Grupo-Monitor-Bodega/monitor_warehouse_master/resources/img/PCBSoldadura.png

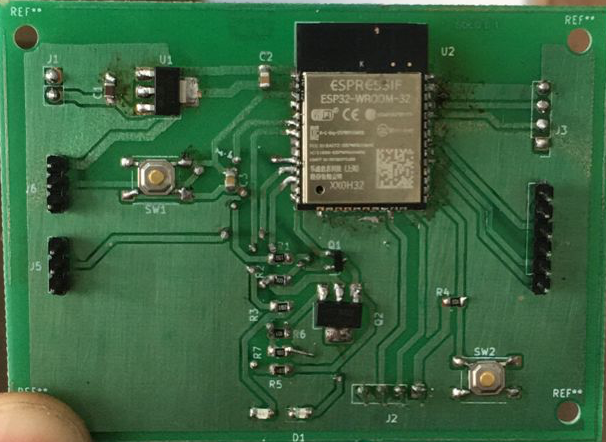
resources/img/PCBSoldadura.png
