Grupo-Monitor-Bodega/monitor_warehouse_master/resources/img/schema_embebed_project.png

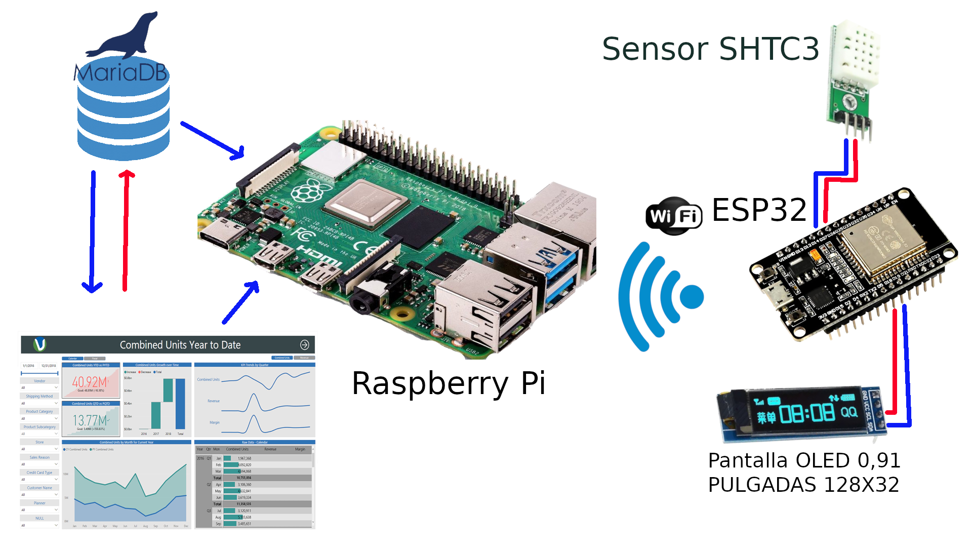
resources/img/schema_embebed_project.png
