Grupo-Monitor-Bodega/monitor_warehouse_master/resources/img/3DPCB01.png

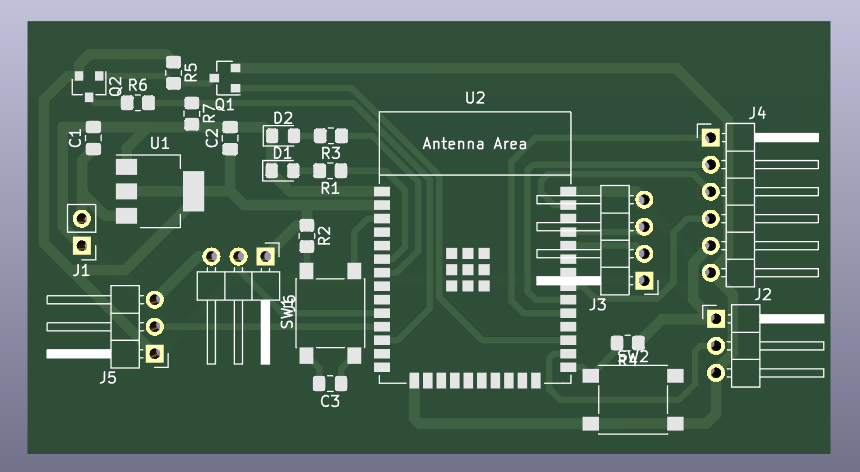
resources/img/3DPCB01.png
