Grupo-Monitor-Bodega/monitor_warehouse_master/resources/img/ConexionLeds-Batería.png

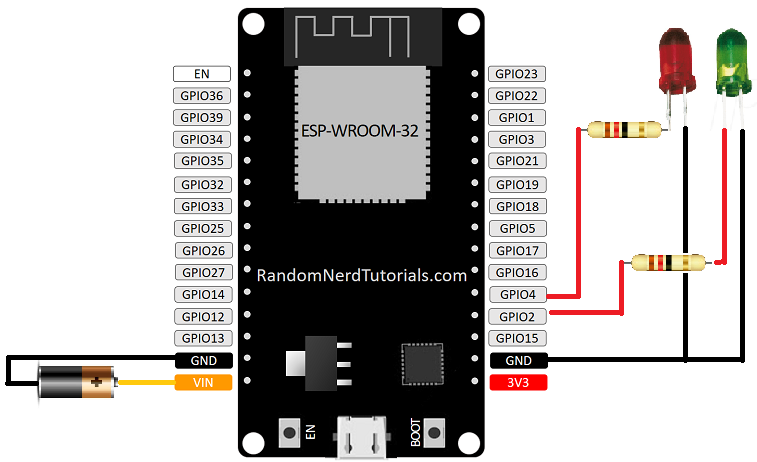
resources/img/ConexionLeds-Batería.png
