Grupo-Monitor-Bodega/monitor_warehouse_master/resources/img/ConexionSD.png

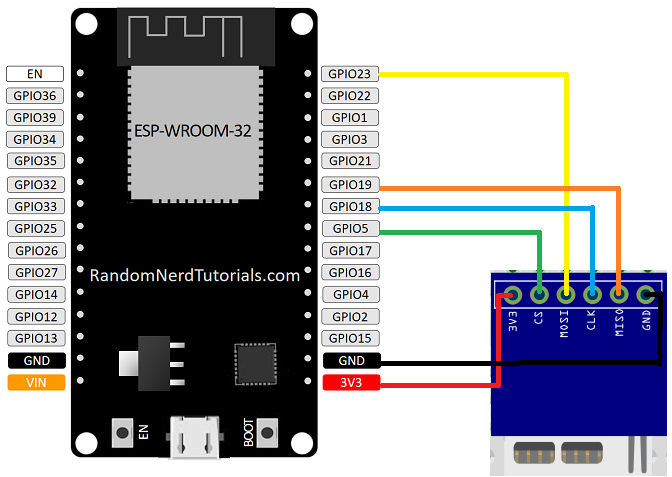
resources/img/ConexionSD.png
