Grupo-Monitor-Bodega/monitor_warehouse_master/resources/img/ConexionSensor.png

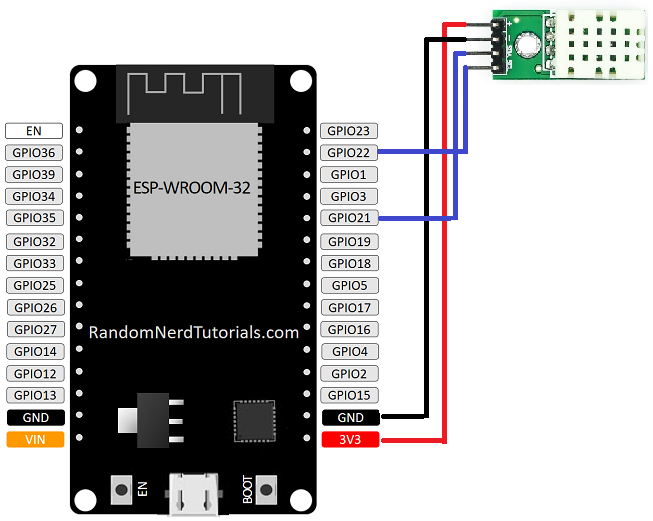
resources/img/ConexionSensor.png
