Grupo-Monitor-Bodega/monitor_warehouse_master/resources/img/Diag_bloques.png

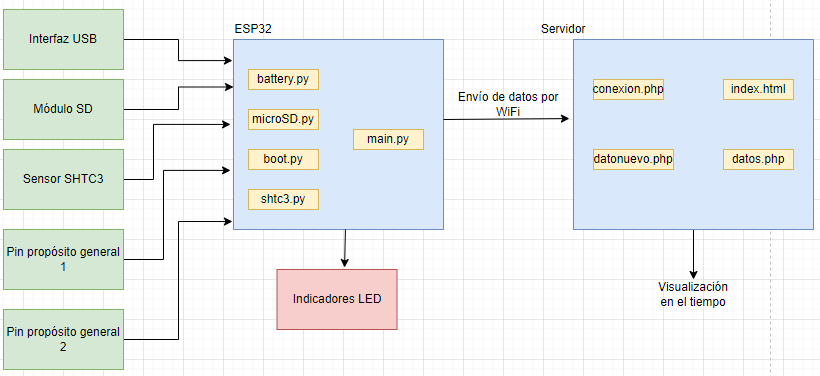
resources/img/Diag_bloques.png
