Grupo-Monitor-Bodega/monitor_warehouse_master/resources/img/esptool.png

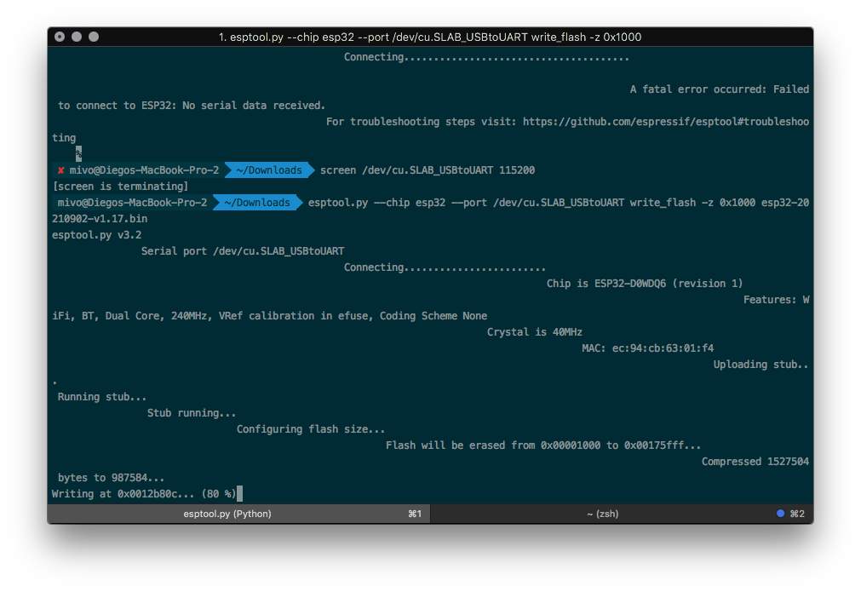
resources/img/esptool.png
