Grupo-Monitor-Bodega/monitor_warehouse_master/resources/img/FinalSchematic2.png

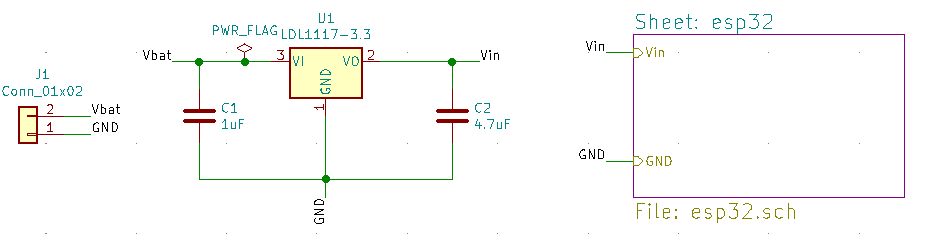
resources/img/FinalSchematic2.png
