Grupo-Monitor-Bodega/monitor_warehouse_master/resources/img/monitor_diagram.drawio.png

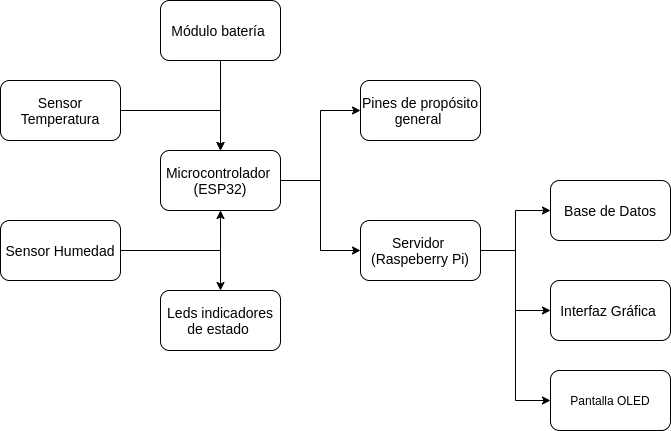
resources/img/monitor_diagram.drawio.png
