Grupo-Monitor-Bodega/monitor_warehouse_master/resources/img/pcb1.png

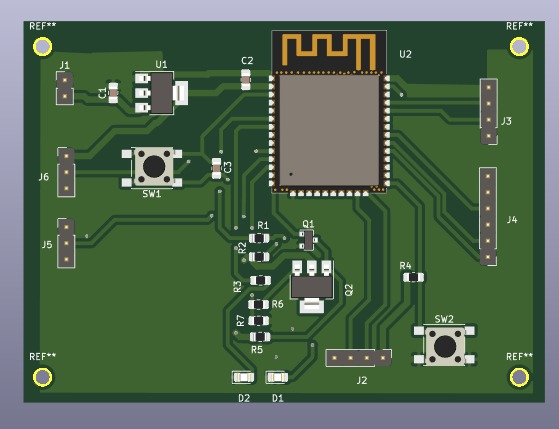
resources/img/pcb1.png
