Grupo-Monitor-Bodega/monitor_warehouse_master/resources/img/PCB01.png

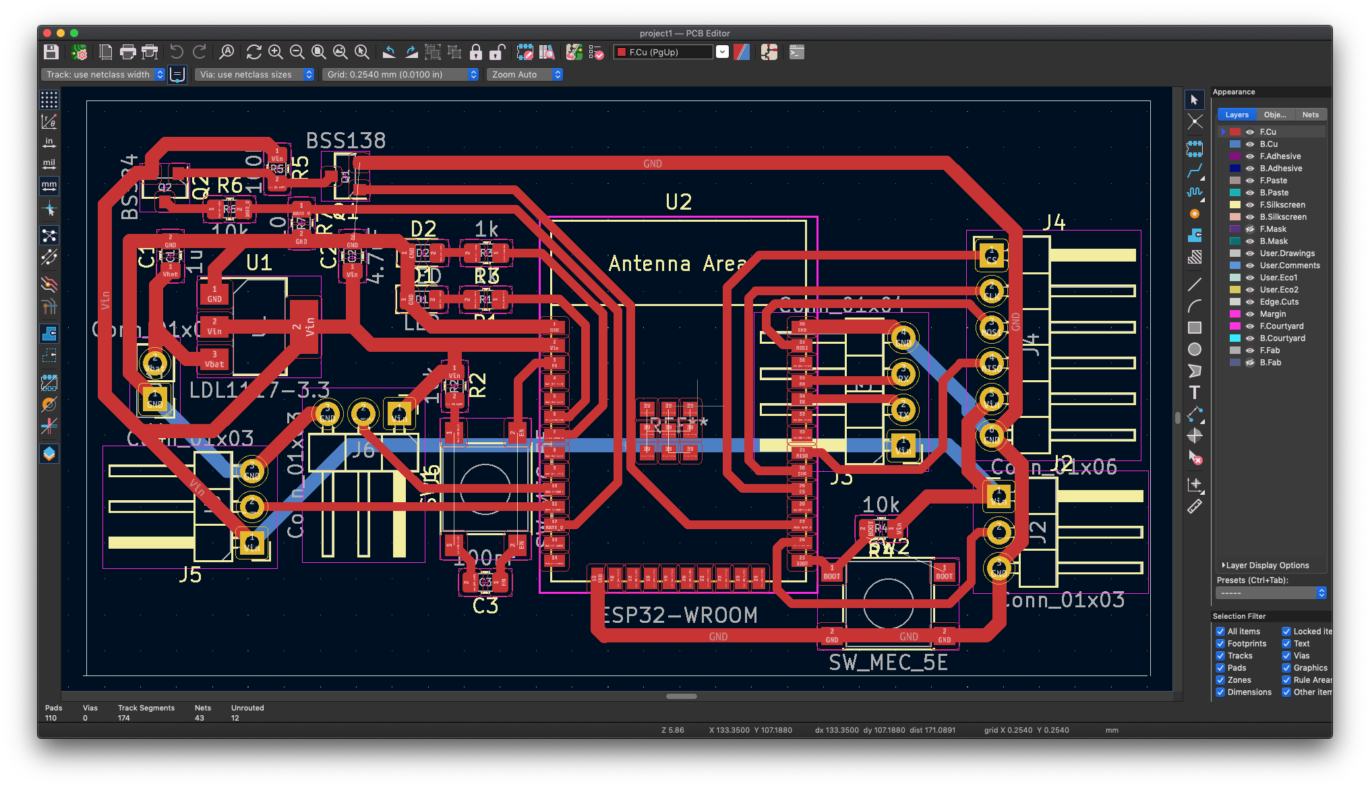
resources/img/PCB01.png
