Grupo-Monitor-Bodega/monitor_warehouse_master/resources/img/pcb2.png

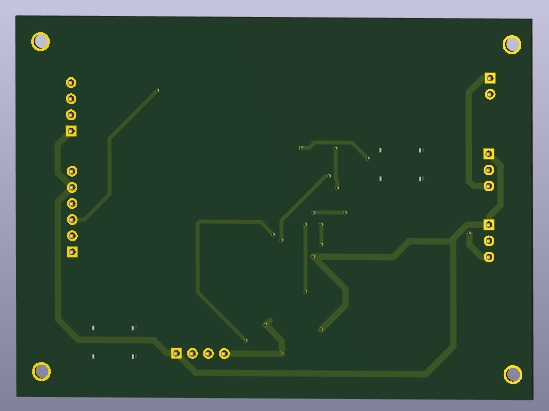
resources/img/pcb2.png
