Grupo-Monitor-Bodega/monitor_warehouse_master/resources/img/pcb3.png

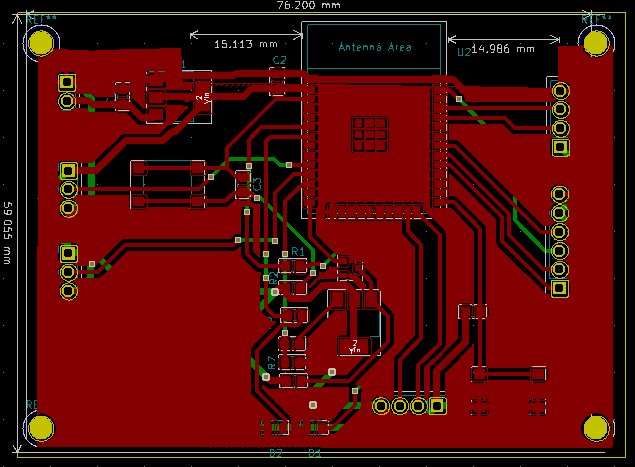
resources/img/pcb3.png
