Grupo-Monitor-Bodega/monitor_warehouse_master/resources/img/pcb4.png

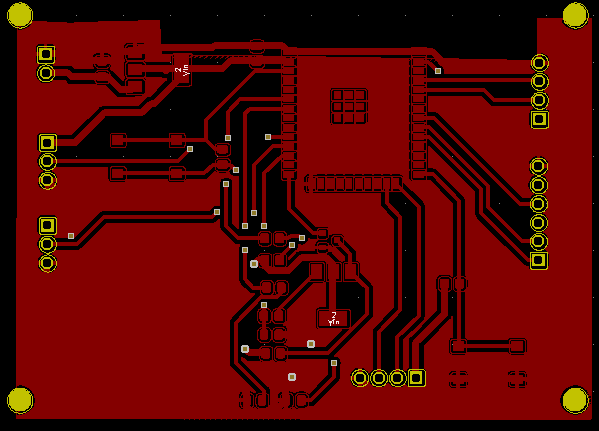
resources/img/pcb4.png
