Grupo-Monitor-Bodega/monitor_warehouse_master/resources/img/pcb5.png

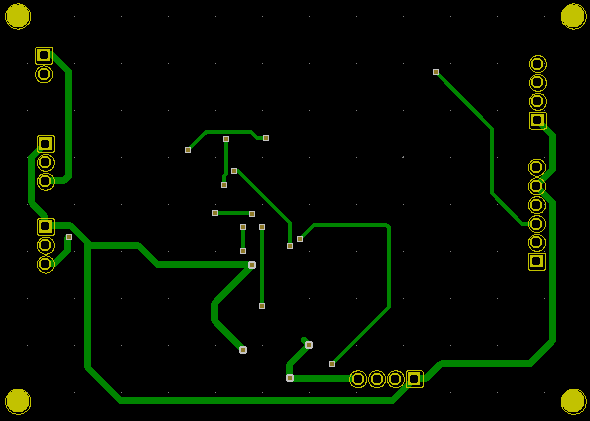
resources/img/pcb5.png
