Grupo-Monitor-Bodega/monitor_warehouse_master/resources/img/pcb6.png

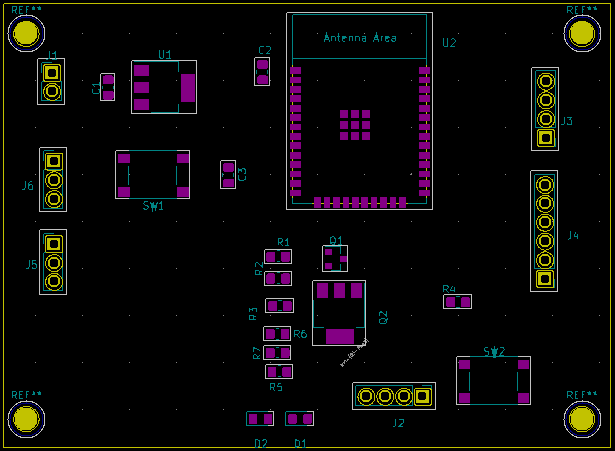
resources/img/pcb6.png
