Grupo-Monitor-Bodega/monitor_warehouse_master/resources/img/pcb7.png

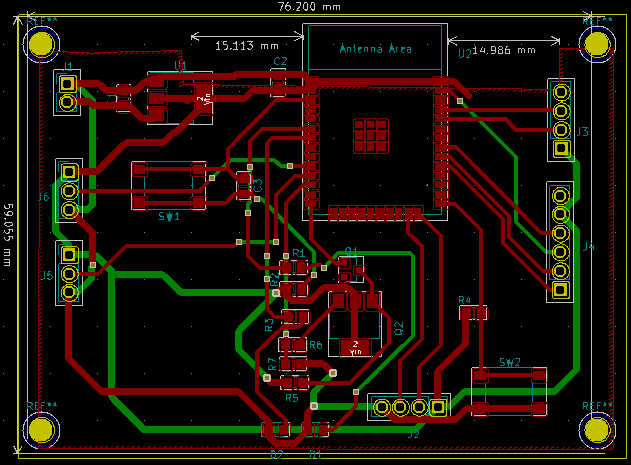
resources/img/pcb7.png
