Grupo-Monitor-Bodega/monitor_warehouse_master/resources/img/pcb8.png

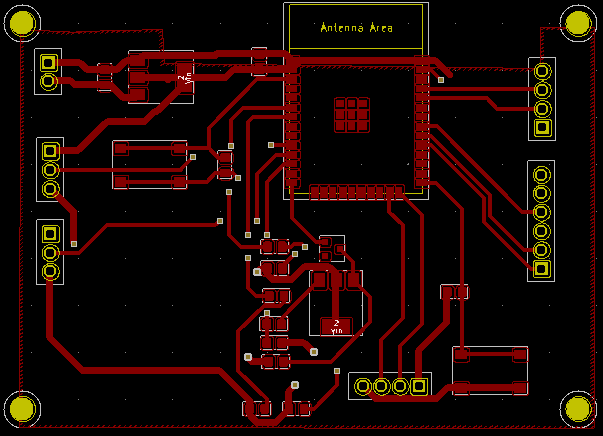
resources/img/pcb8.png
