Grupo-Monitor-Bodega/monitor_warehouse_master/resources/img/PCBdone1.jpeg

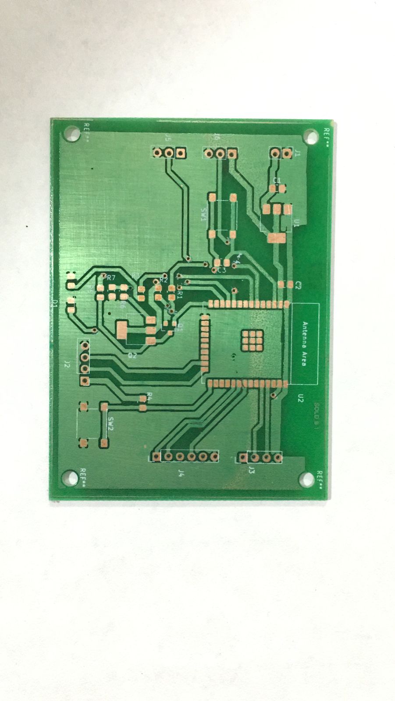
resources/img/PCBdone1.jpeg
