Grupo-Monitor-Bodega/monitor_warehouse_master/resources/img/PCBdone2.jpeg

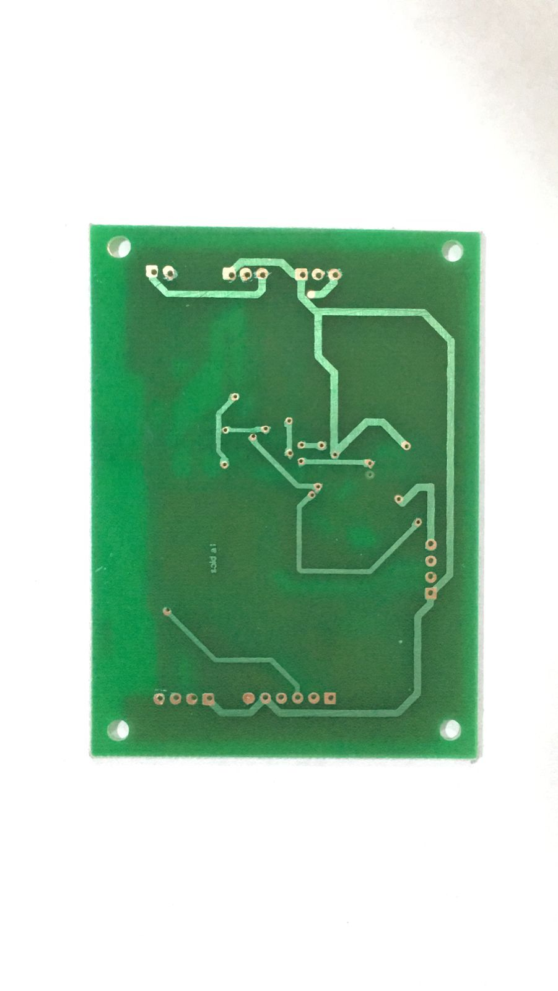
resources/img/PCBdone2.jpeg
