Grupo-Monitor-Bodega/monitor_warehouse_master/resources/img/Schematic4.png

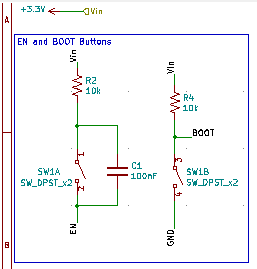
resources/img/Schematic4.png
