Grupo-Monitor-Bodega/monitor_warehouse_master/resources/img/Schematic5.png

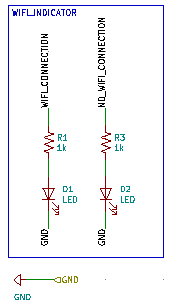
resources/img/Schematic5.png
