Grupo-Monitor-Bodega/monitor_warehouse_master/resources/img/Schematic8.png

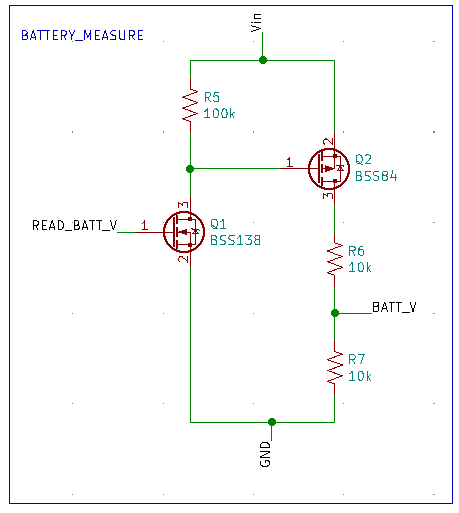
resources/img/Schematic8.png
