Grupo-Monitor-Bodega/monitor_warehouse_master/resources/img/screen.png

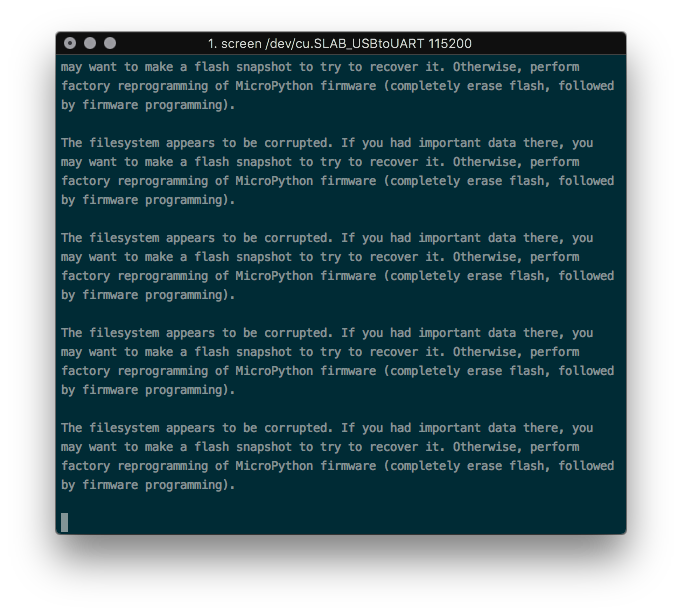
resources/img/screen.png
