Grupo-Monitor-Bodega/monitor_warehouse_master/resources/img/Servidor.png

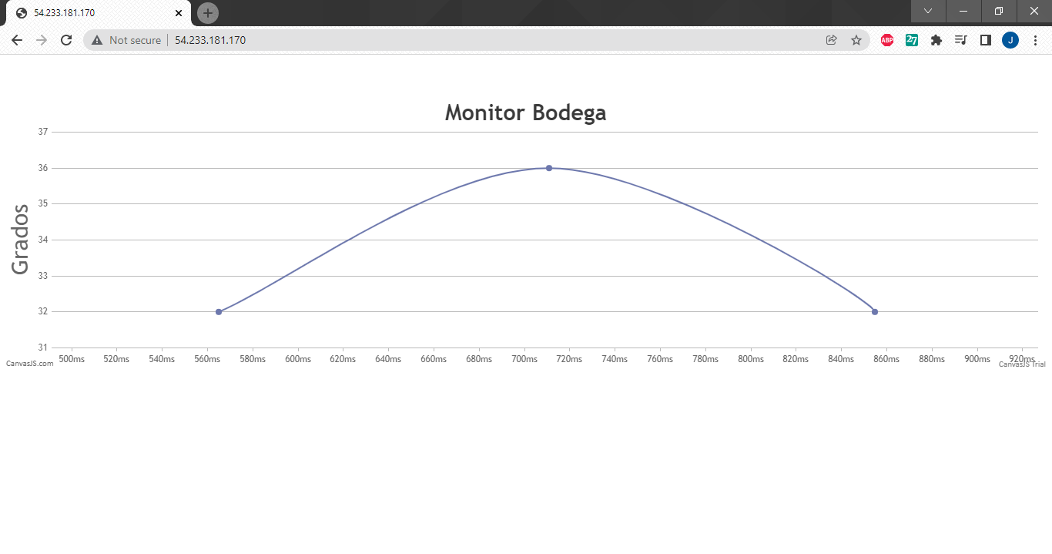
resources/img/Servidor.png
