Grupo-Monitor-Bodega/monitor_warehouse_master/resources/img/Test_servidor.png

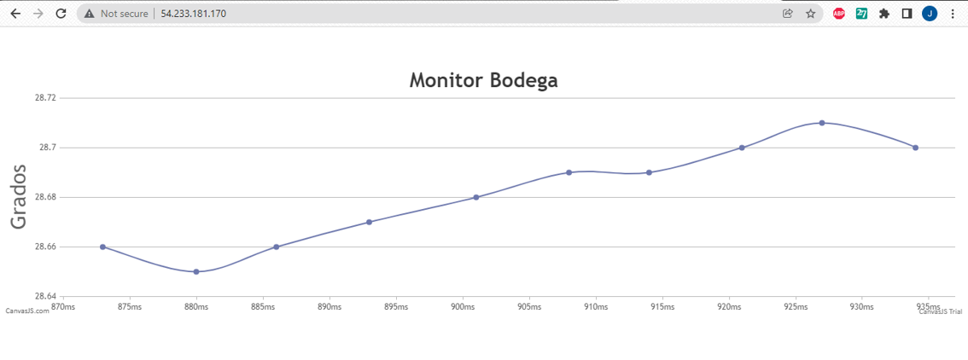
resources/img/Test_servidor.png
