Grupo-Monitor-Bodega/monitor_warehouse_master/resources/img/IMG_9449.JPG

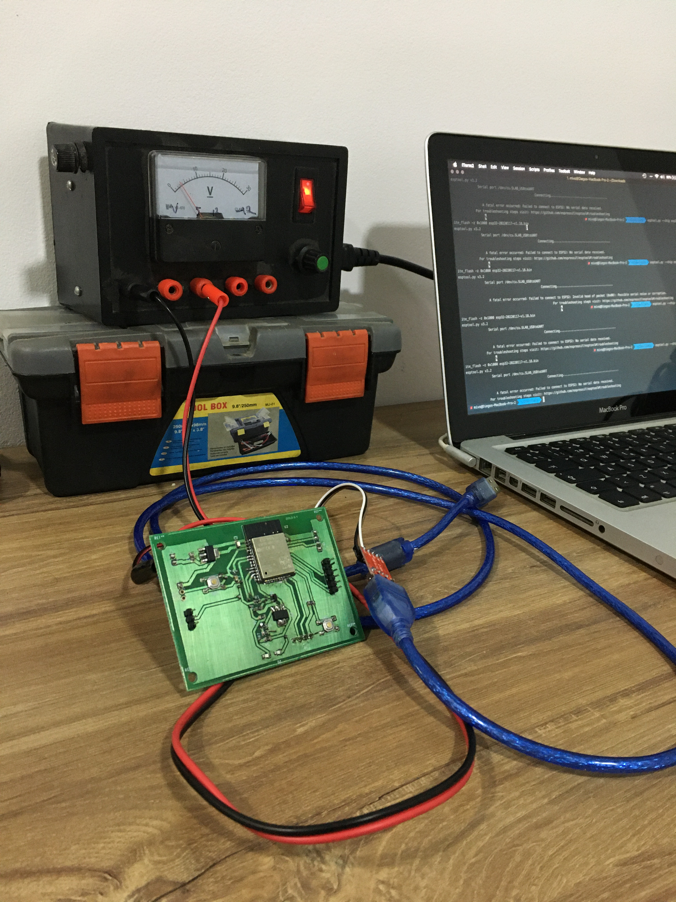
resources/img/IMG_9449.JPG
